JesseDiaz47/esp32-power-pack-case/renders/preview.png

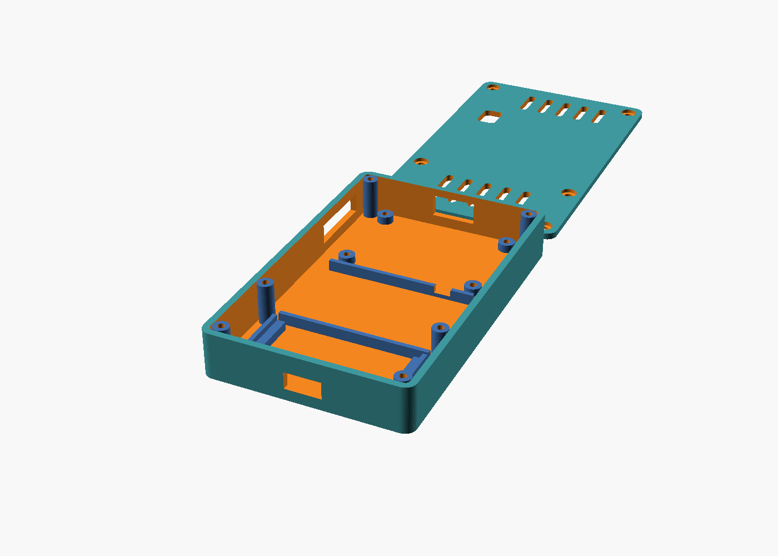
renders/preview.png
